svenpetersen1965/VIC-20_AV-Adapter/3Dprinted_case/Rev. 2/label/label_col.png

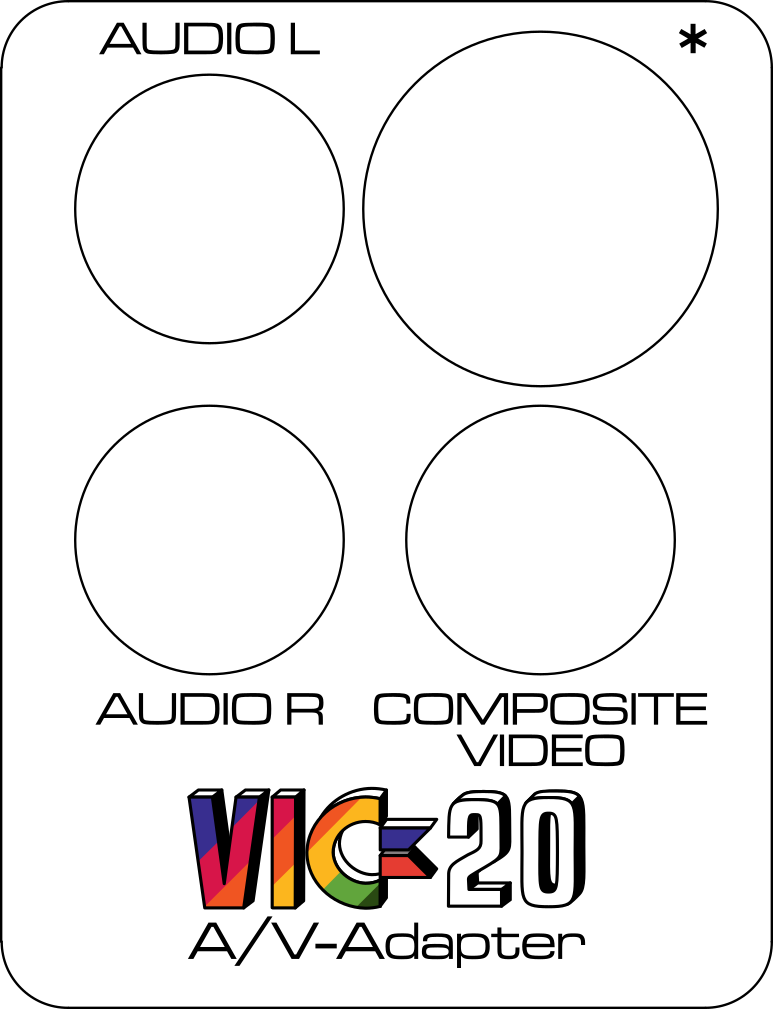
3Dprinted_case/Rev. 2/label/label_col.png
