svenpetersen1965/VIC-20_AV-Adapter/Rev. 0/pictures/8903_Penultimate_Menu.JPG

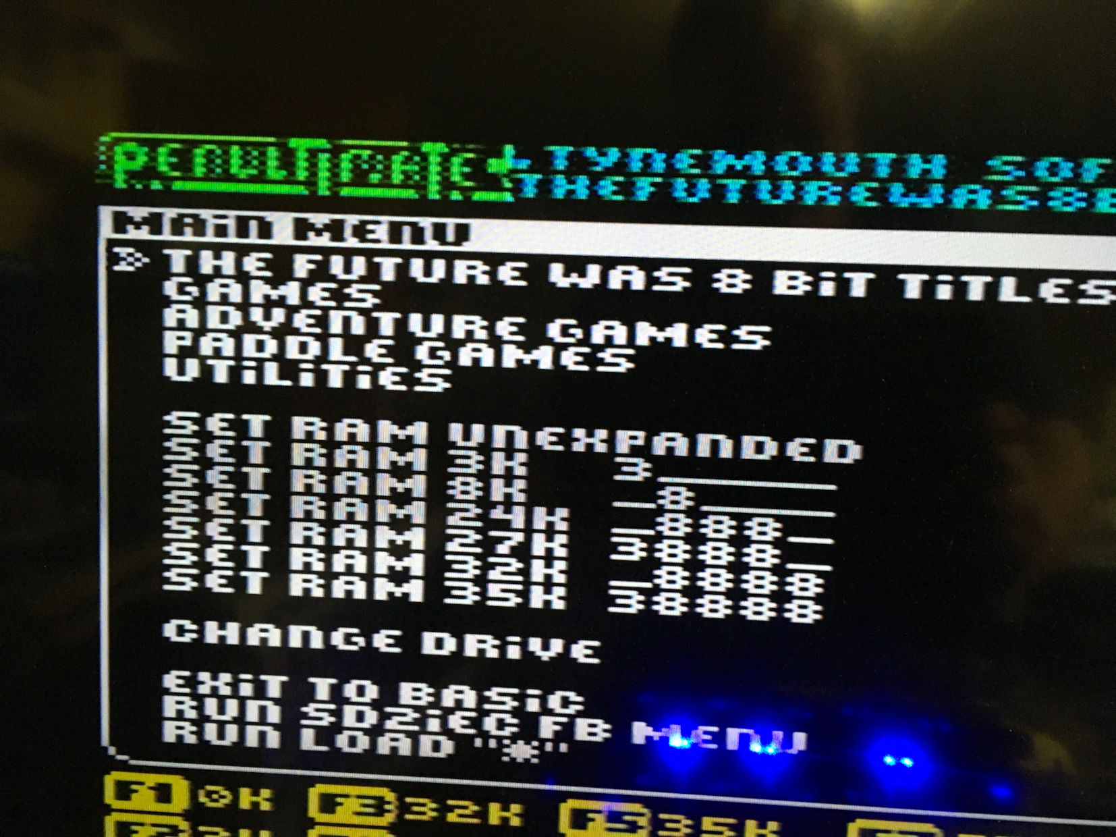
Rev. 0/pictures/8903_Penultimate_Menu.JPG
