svenpetersen1965/VIC-20_AV-Adapter/Rev. 0/pictures/9041_-_ATARI_800XL_Display.JPG

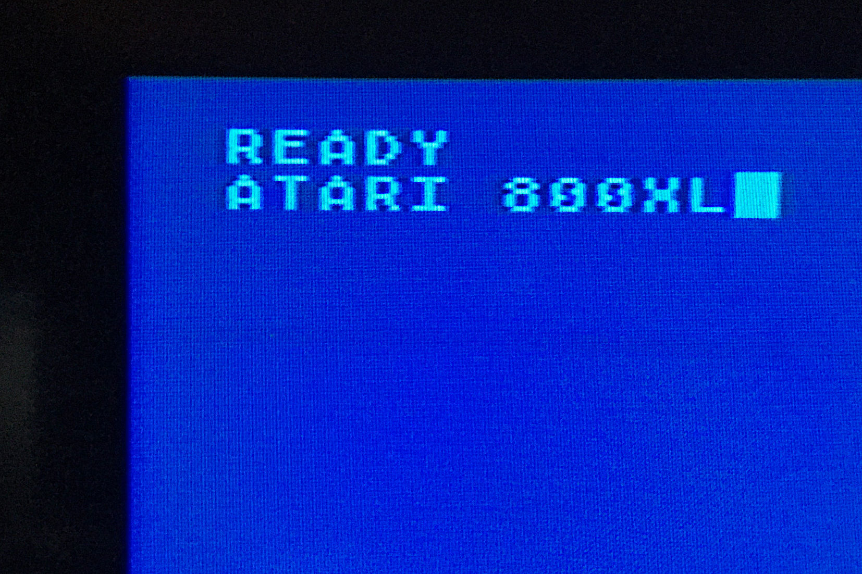
Rev. 0/pictures/9041_-_ATARI_800XL_Display.JPG
