svenpetersen1965/VIC-20_AV-Adapter/Rev. 0/pictures/C64_screen.jpg

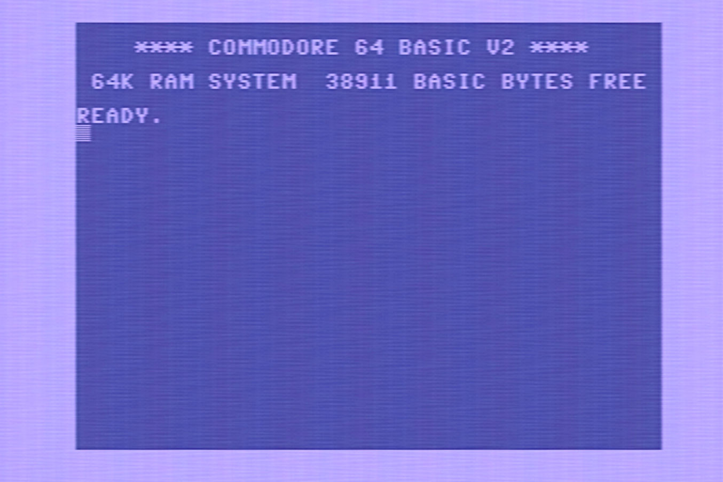
Rev. 0/pictures/C64_screen.jpg
