svenpetersen1965/VIC-20_AV-Adapter/Rev. 2/pictures/0050_-_Vicky20_composite.JPG

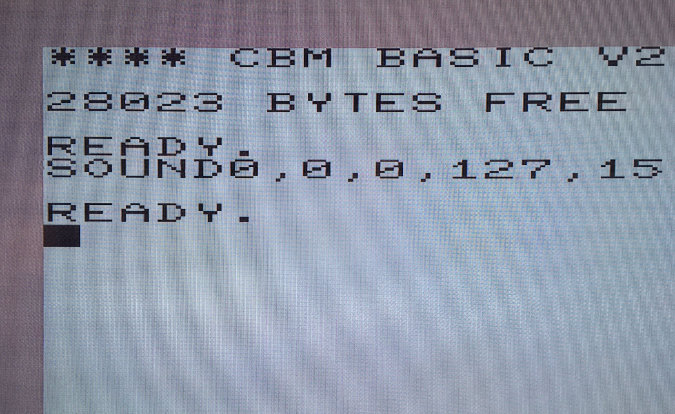
Rev. 2/pictures/0050_-_Vicky20_composite.JPG
