svenpetersen1965/VIC-20_AV-Adapter/Rev. 2/pictures/0052_-_BASIC_S-Video.JPG

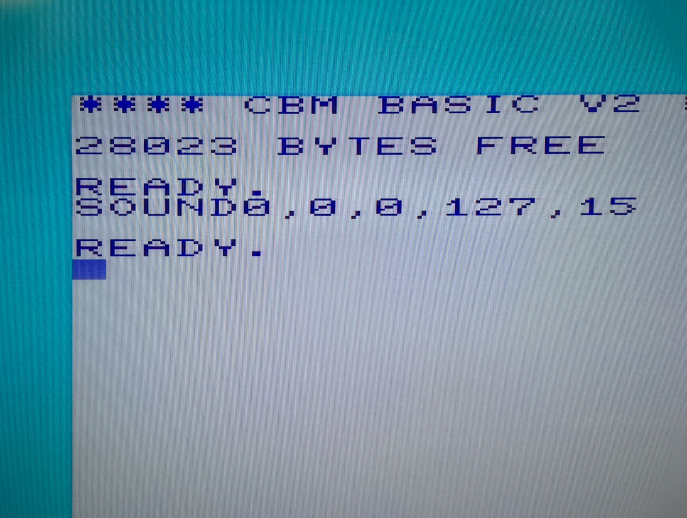
Rev. 2/pictures/0052_-_BASIC_S-Video.JPG
