svenpetersen1965/VIC-20_AV-Adapter/Rev. 2/pictures/0186_-_C64_Composite.JPG

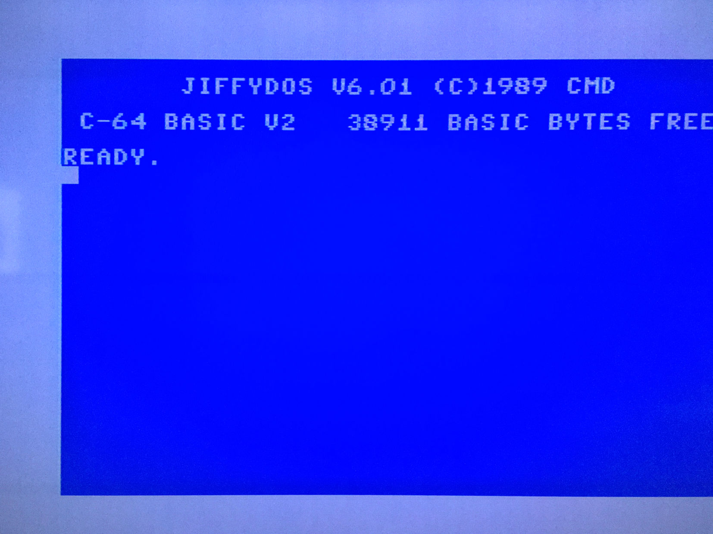
Rev. 2/pictures/0186_-_C64_Composite.JPG
