svenpetersen1965/VIC-20_AV-Adapter/Rev. 2/pictures/0187_-_C64_S-Video.JPG

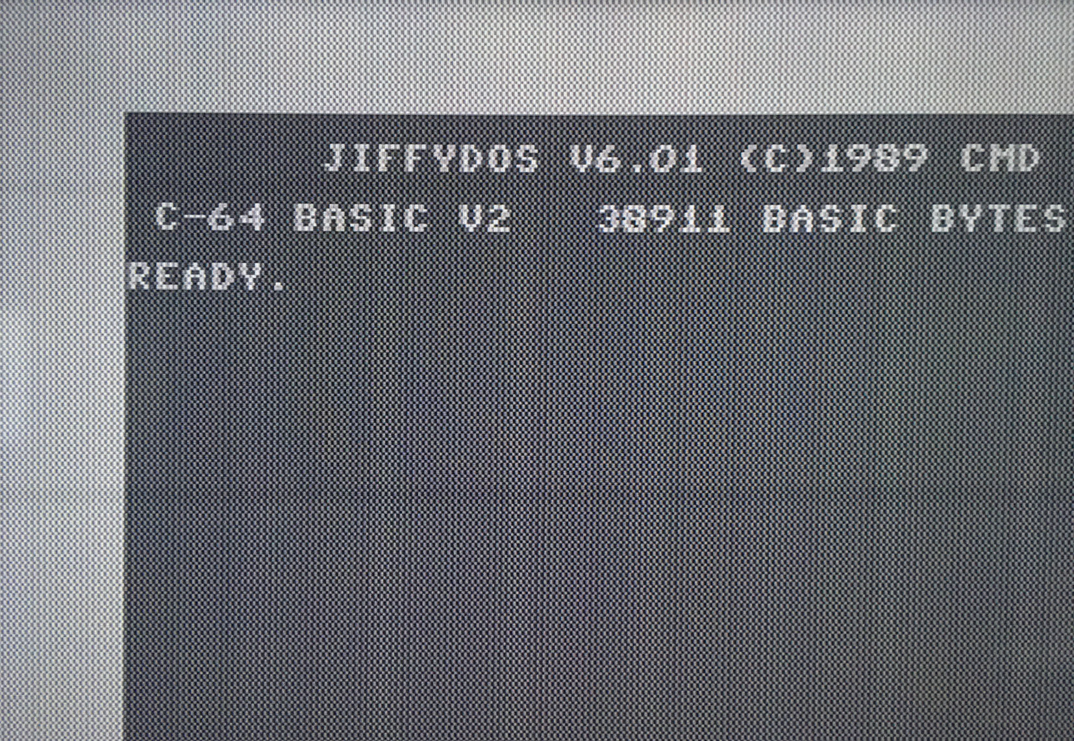
Rev. 2/pictures/0187_-_C64_S-Video.JPG
