svenpetersen1965/VIC-20_AV-Adapter/Rev. 2/pictures/0191_-_VIC20CR_Composite.JPG

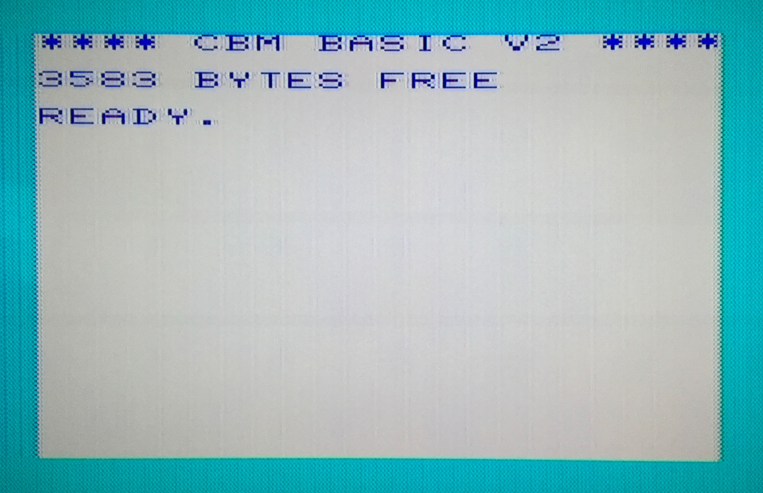
Rev. 2/pictures/0191_-_VIC20CR_Composite.JPG
