svenpetersen1965/VIC-20_AV-Adapter/Rev. 2/pictures/0193_-_VIC20CR_s-video.JPG

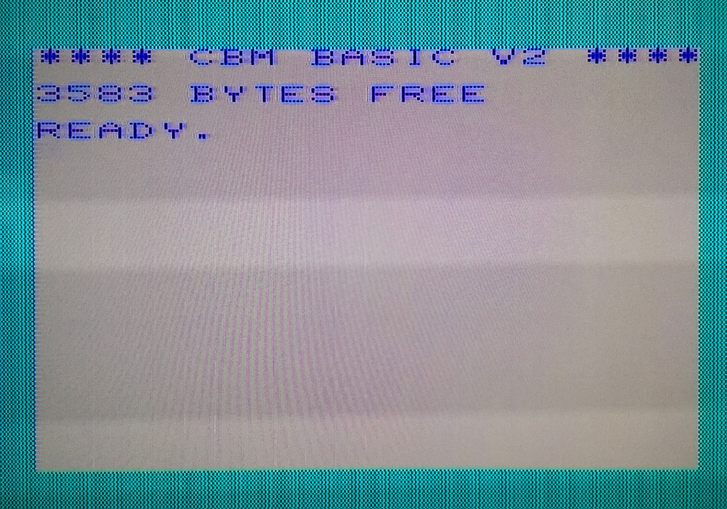
Rev. 2/pictures/0193_-_VIC20CR_s-video.JPG
