svenpetersen1965/VIC-20_AV-Adapter/Rev. 2/pictures/0195_-_VIC20_2pr_composite.JPG

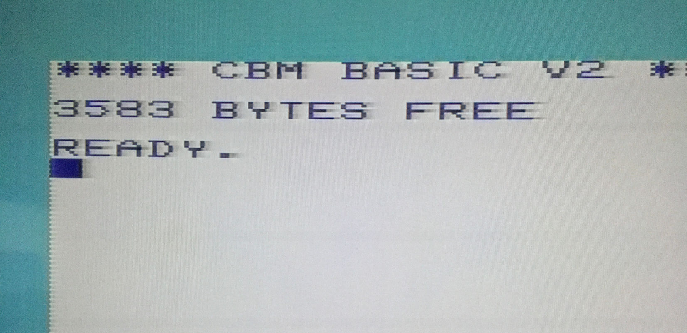
Rev. 2/pictures/0195_-_VIC20_2pr_composite.JPG
