svenpetersen1965/VIC-20_AV-Adapter/Rev. 2/pictures/Comp_DONK.jpg

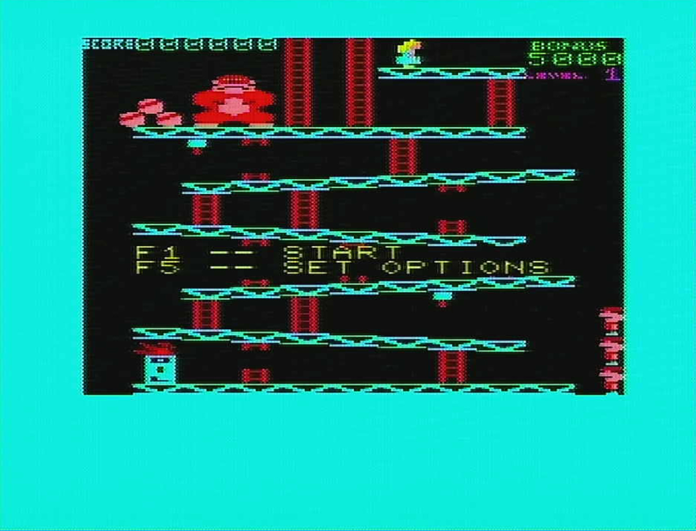
Rev. 2/pictures/Comp_DONK.jpg
