svenpetersen1965/VIC-20_AV-Adapter/Rev. 2/pictures/Comp_PUC.jpg

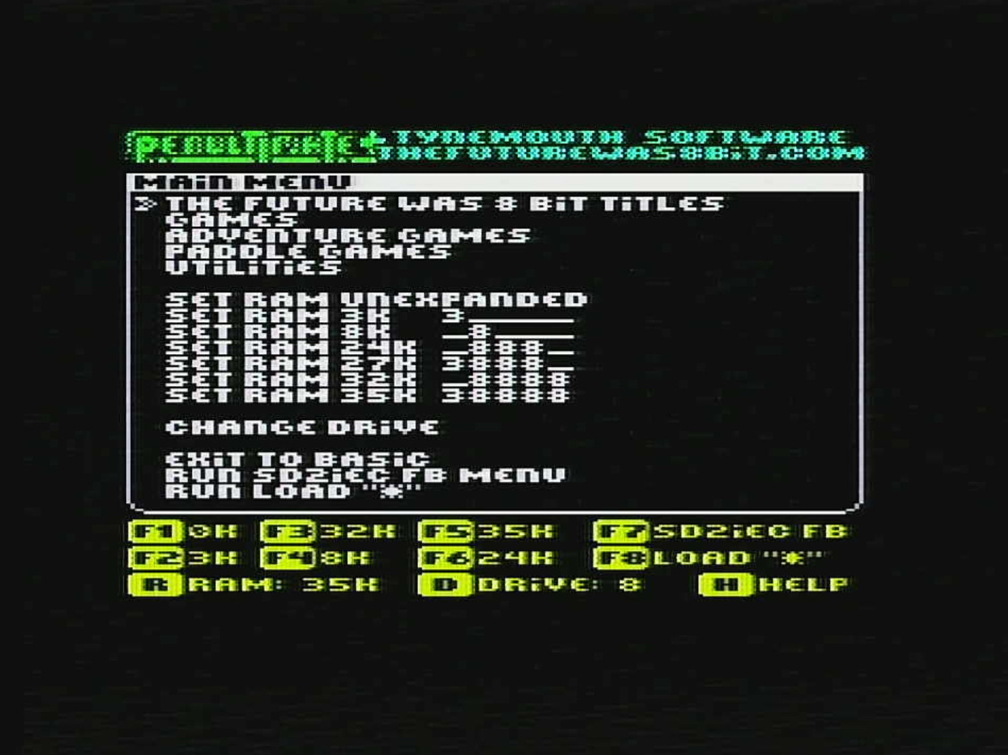
Rev. 2/pictures/Comp_PUC.jpg
