svenpetersen1965/VIC-20_AV-Adapter/Rev. 2/pictures/IMG_2774.JPG

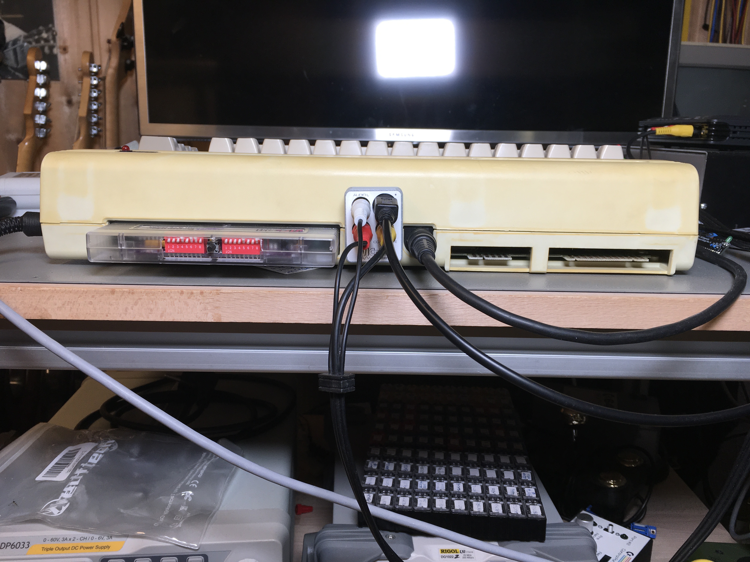
Rev. 2/pictures/IMG_2774.JPG
