svenpetersen1965/VIC-20_AV-Adapter/Rev. 2/pictures/S-video_BASIC.jpg

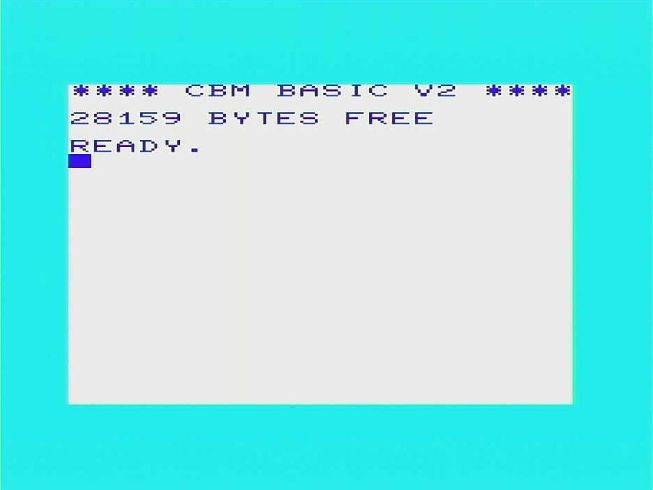
Rev. 2/pictures/S-video_BASIC.jpg
