svenpetersen1965/VIC-20_AV-Adapter/Rev. 2/pictures/S-Video_DONK.jpg

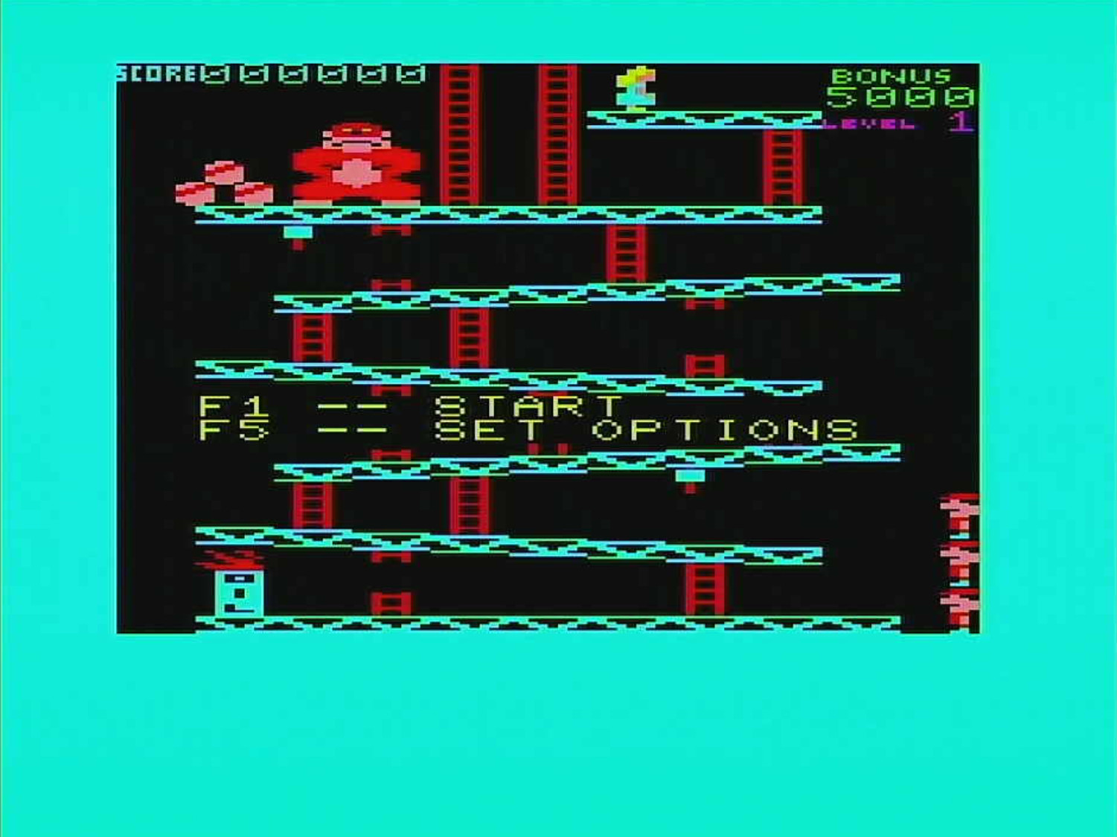
Rev. 2/pictures/S-Video_DONK.jpg
