svenpetersen1965/VIC-20_AV-Adapter/Rev. 2/pictures/S-Video_PUC.jpg

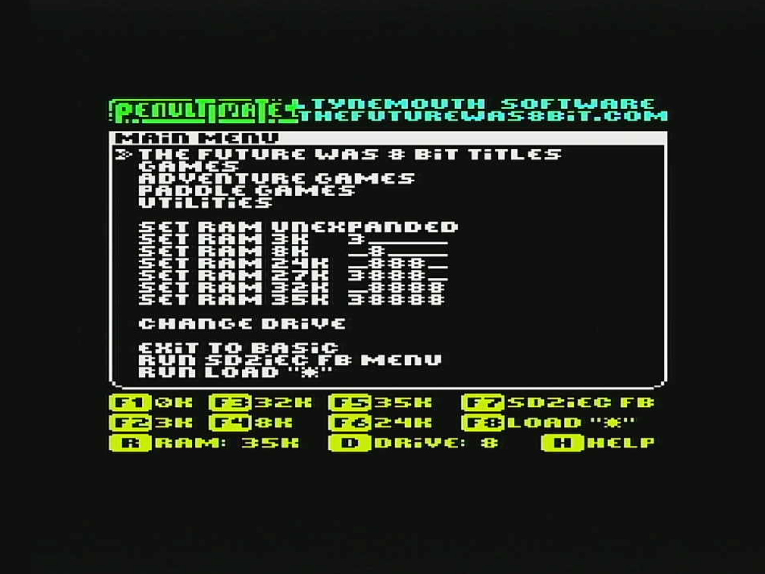
Rev. 2/pictures/S-Video_PUC.jpg
