svenpetersen1965/VIC-20_AV-Adapter/Rev. 0/dxf/VIC-20_AV-Adaptor_bot.dxf

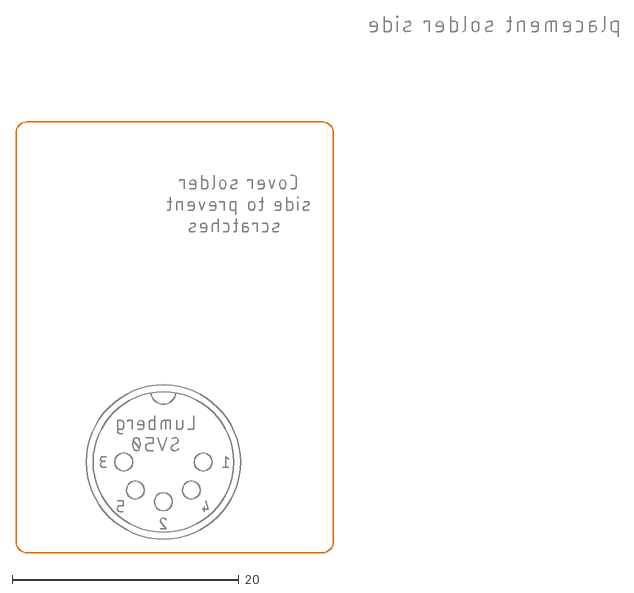
[picture p101: CAD file, 2021-07-19, an earlier design]
Rev. 0/dxf/VIC-20_AV-Adaptor_bot.dxf
53.1 x 47.3
