svenpetersen1965/VIC-20_AV-Adapter/Rev. 0/dxf/VIC-20_AV-Adaptor_top.dxf

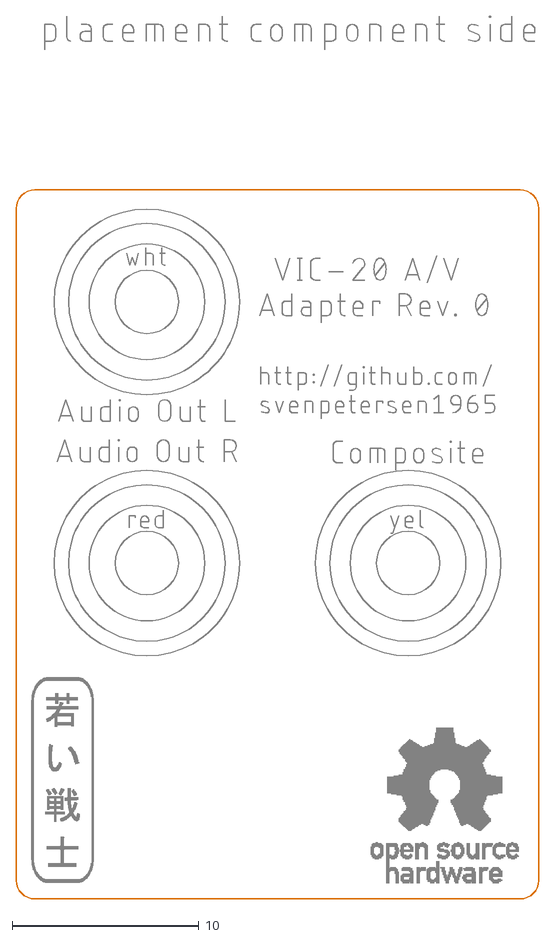
[picture p102: CAD file, 2021-07-19, an earlier design]
Rev. 0/dxf/VIC-20_AV-Adaptor_top.dxf
28.0 x 47.3
