svenpetersen1965/VIC-20_AV-Adapter/Rev. 0/pictures/8935_-_Test_VIC-20CR.JPG

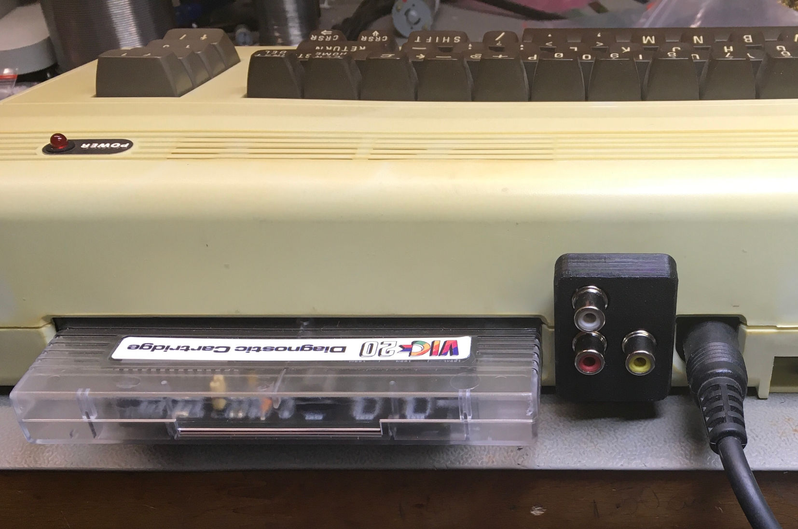
Rev. 0/pictures/8935_-_Test_VIC-20CR.JPG
